Lionel-Lim/ClothSense/resource/img/coverAndBase.jpeg

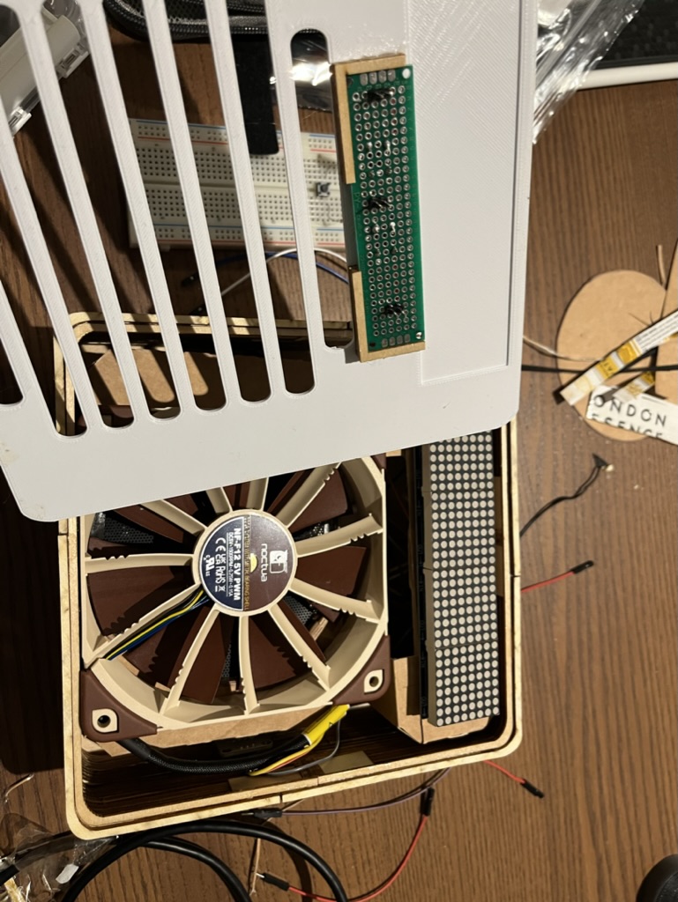
resource/img/coverAndBase.jpeg
