Lionel-Lim/ClothSense/resource/img/lasercutBracket.jpeg

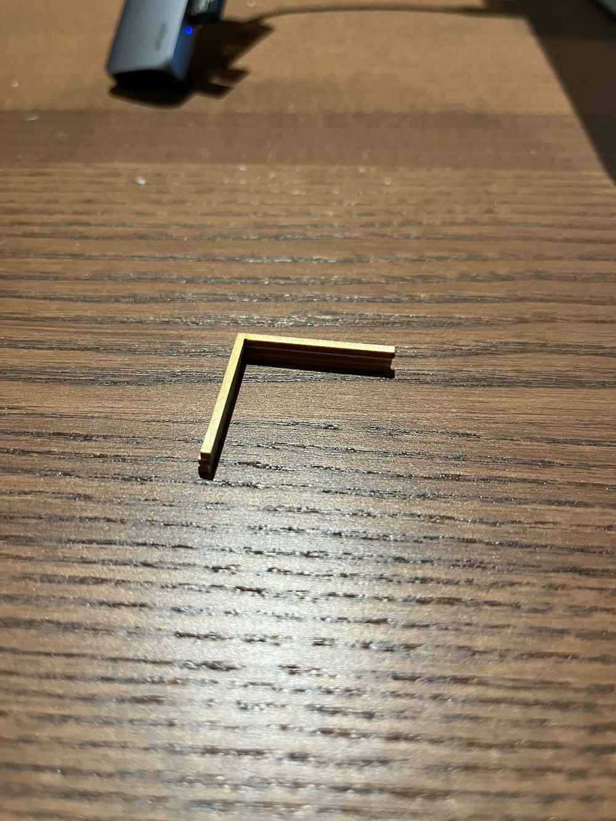
resource/img/lasercutBracket.jpeg
