Lionel-Lim/ClothSense/resource/getSerial/result/drying_2.csv

Test at 17:52 |  |  |  | y = 2E-10x3 - 2E-06x2 + 0.0058x + 49.68
21 | 50 | 5003 | 00:00:05.3 | 299.965
21 | 51 | 10004 | 00:00:10.4
21 | 51 | 15003 | 00:00:15.3
21 | 51 | 20004 | 00:00:20.4
21 | 51 | 25004 | 00:00:25.4
21 | 51 | 30003 | 00:00:30.3
21 | 52 | 35003 | 00:00:35.3
21 | 52 | 40003 | 00:00:40.3
21 | 52 | 45003 | 00:00:45.3
21 | 52 | 50003 | 00:00:50.3
21 | 52 | 55003 | 00:00:55.3
21 | 52 | 60003 | 00:01:00.3
21 | 52 | 65003 | 00:01:05.3
21 | 53 | 70003 | 00:01:10.3
21 | 52 | 75003 | 00:01:15.3
21 | 52 | 80003 | 00:01:20.3
21 | 52 | 85003 | 00:01:25.3
21 | 52 | 90003 | 00:01:30.3
21 | 52 | 95003 | 00:01:35.3
21 | 52 | 100003 | 00:01:40.3
21 | 52 | 105008 | 00:01:45.8
21 | 52 | 110003 | 00:01:50.3
21 | 52 | 115003 | 00:01:55.3
21 | 52 | 120004 | 00:02:00.4
21 | 52 | 125003 | 00:02:05.3
21 | 53 | 130003 | 00:02:10.3
20 | 53 | 135003 | 00:02:15.3
20 | 53 | 140003 | 00:02:20.3
20 | 53 | 145003 | 00:02:25.3
20 | 52 | 150003 | 00:02:30.3
20 | 52 | 155003 | 00:02:35.3
20 | 52 | 160003 | 00:02:40.3
20 | 52 | 165003 | 00:02:45.3
20 | 52 | 170003 | 00:02:50.3
20 | 52 | 175003 | 00:02:55.3
21 | 52 | 180003 | 00:03:00.3
20 | 52 | 185004 | 00:03:05.4
20 | 52 | 190003 | 00:03:10.3
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
