Lionel-Lim/ClothSense/resource/getSerial/result/drying_calculation.xlsx

20 | 49 | 5003 | 00:00:05.3 | 53.00041848 | Min Temp | 20 | Min Hum | 49
20 | 49 | 10004 | 00:00:10.4 | 53.00083641 | Max Temp | 21 | Max Hum | 57
20 | 49 | 5003 | 00:00:05.3 | 53.00125379
20 | 49 | 10003 | 00:00:10.3 | 53.00167063
20 | 49 | 15003 | 00:00:15.3 | 53.00208692
20 | 49 | 20003 | 00:00:20.3 | 53.00250266
20 | 49 | 25004 | 00:00:25.4 | 53.00291786
20 | 49 | 30003 | 00:00:30.3 | 53.00333251
20 | 49 | 35003 | 00:00:35.3 | 53.00374661
20 | 49 | 40004 | 00:00:40.4 | 53.00416017
20 | 49 | 45003 | 00:00:45.3 | 53.00457318
20 | 49 | 50003 | 00:00:50.3 | 53.00498564
20 | 50 | 55003 | 00:00:55.3 | 53.00539756
20 | 50 | 60003 | 00:01:00.3 | 53.00580893
20 | 50 | 65003 | 00:01:05.3 | 53.00621975
20 | 49 | 70003 | 00:01:10.3 | 53.00663003
20 | 49 | 75003 | 00:01:15.3 | 53.00703976
20 | 49 | 80005 | 00:01:20.5 | 53.00744894
20 | 49 | 85003 | 00:01:25.3 | 53.00785758
20 | 50 | 90003 | 00:01:30.3 | 53.00826567
20 | 50 | 95003 | 00:01:35.3 | 53.00867322
20 | 49 | 100003 | 00:01:40.3 | 53.00908021
20 | 49 | 105004 | 00:01:45.4 | 53.00948666
20 | 49 | 110003 | 00:01:50.3 | 53.00989257
20 | 49 | 115003 | 00:01:55.3 | 53.01029792
20 | 49 | 120003 | 00:02:00.3 | 53.01070274
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
